fajarlabs/PROJECT_FloodMonitoring/BOX_PANEL2.jpeg

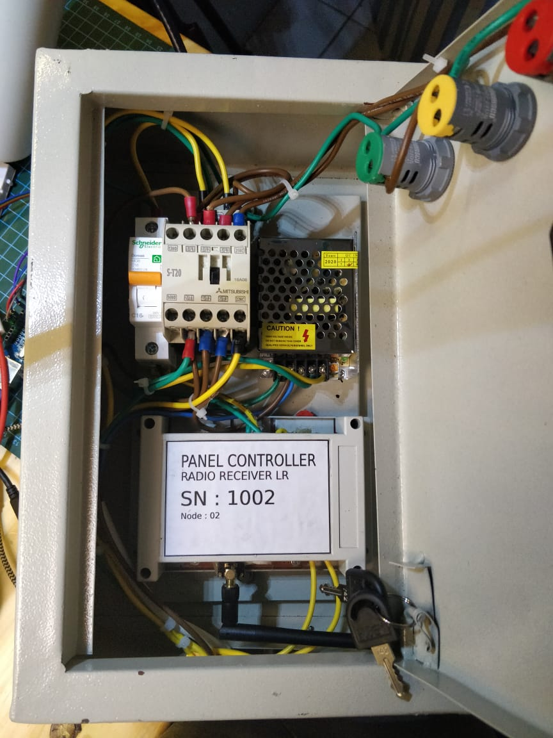
BOX_PANEL2.jpeg
