fajarlabs/PROJECT_FloodMonitoring/BOX_PANEL_FLASH.jpeg

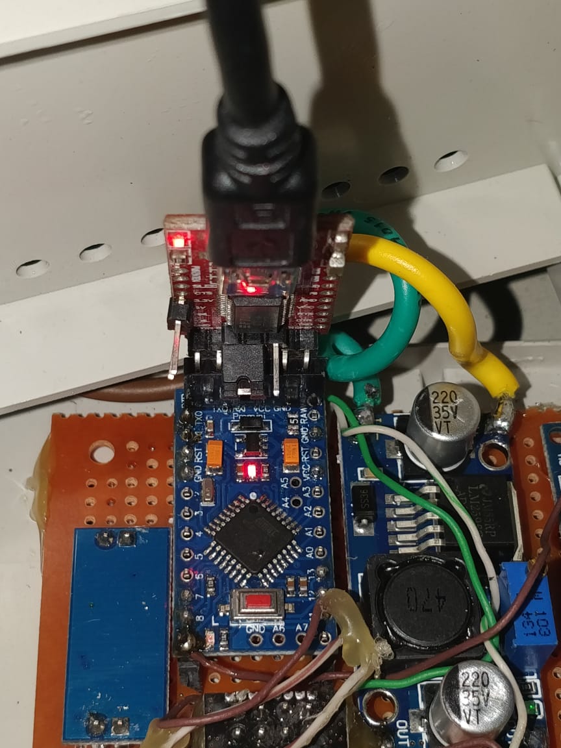
BOX_PANEL_FLASH.jpeg
