fajarlabs/PROJECT_FloodMonitoring/CEK TIMEOUT.png

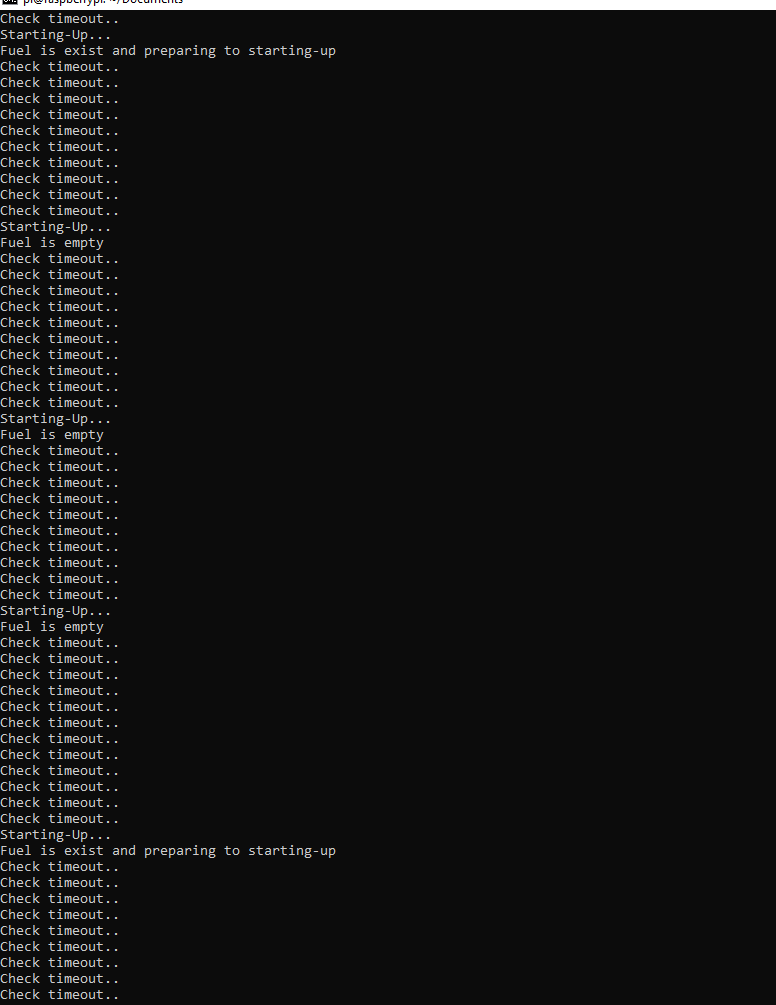
CEK TIMEOUT.png
