fajarlabs/PROJECT_FloodMonitoring/check_timout.png

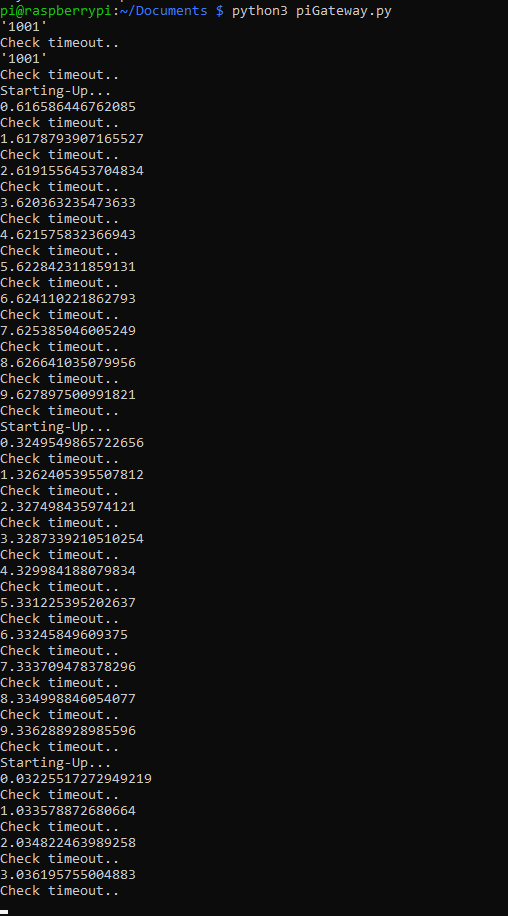
check_timout.png
