fajarlabs/PROJECT_FloodMonitoring/CommandPush.png

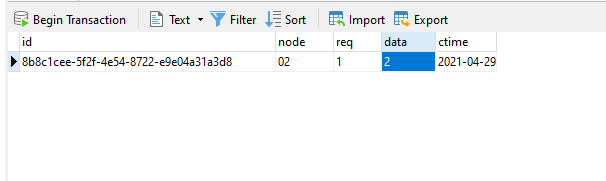
CommandPush.png
