fajarlabs/PROJECT_FloodMonitoring/dataLogController.png

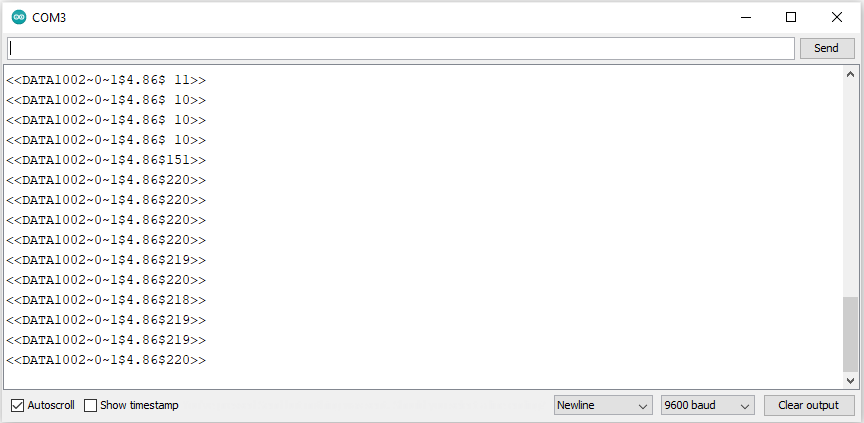
dataLogController.png
