fajarlabs/PROJECT_FloodMonitoring/DB_POSTGRES.png

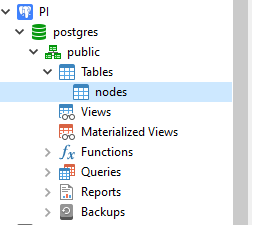
DB_POSTGRES.png
