fajarlabs/PROJECT_FloodMonitoring/Fritzing/COMMAND_CENTER_bb.png

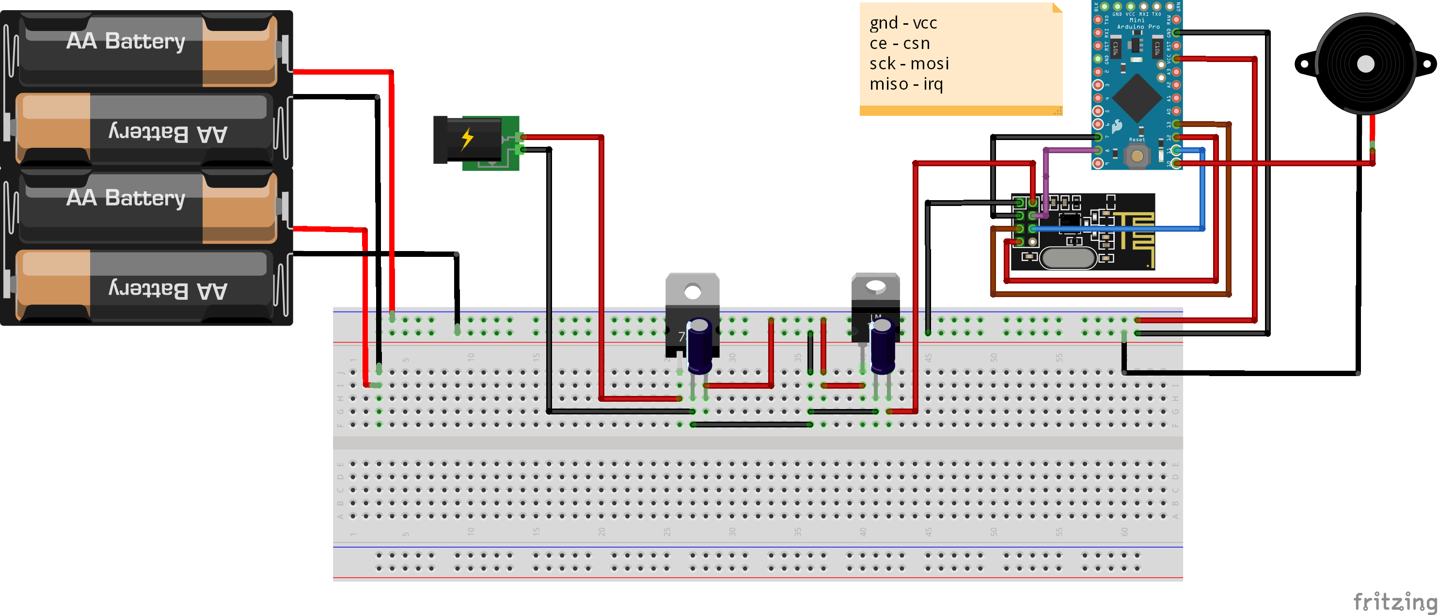
Fritzing/COMMAND_CENTER_bb.png
