fajarlabs/PROJECT_FloodMonitoring/Fritzing/FLOAT_SENSOR.png

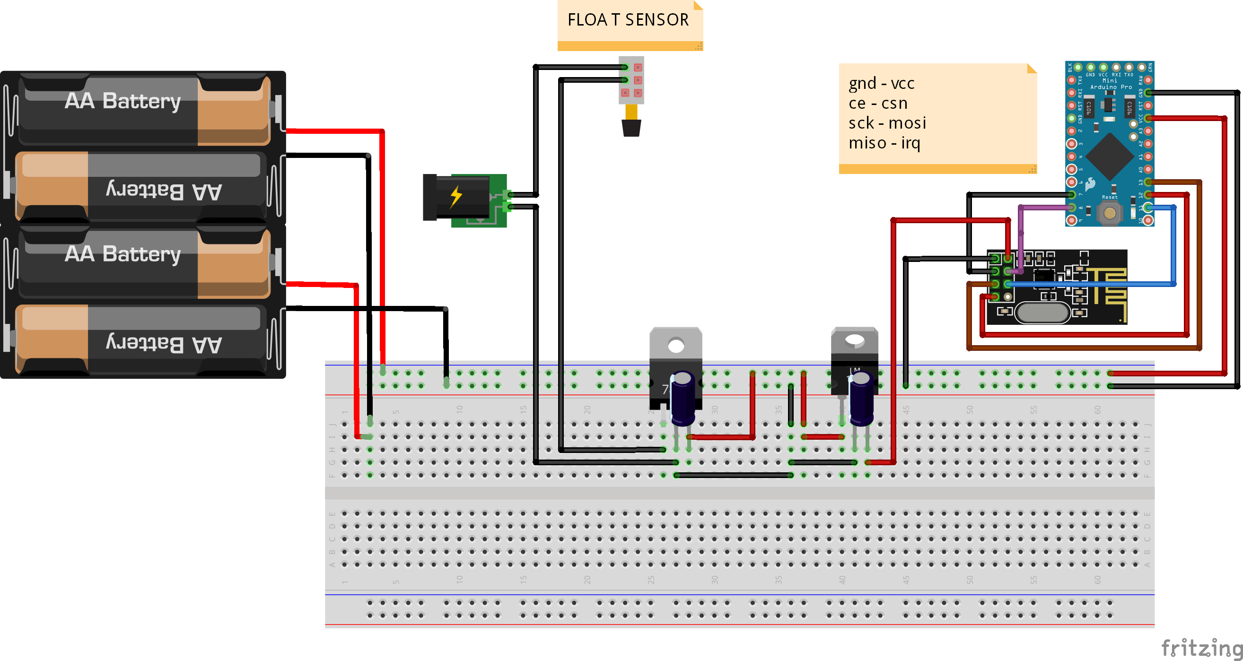
Fritzing/FLOAT_SENSOR.png
