fajarlabs/PROJECT_FloodMonitoring/Fritzing/PANEL_CONTROLLER_bb.png

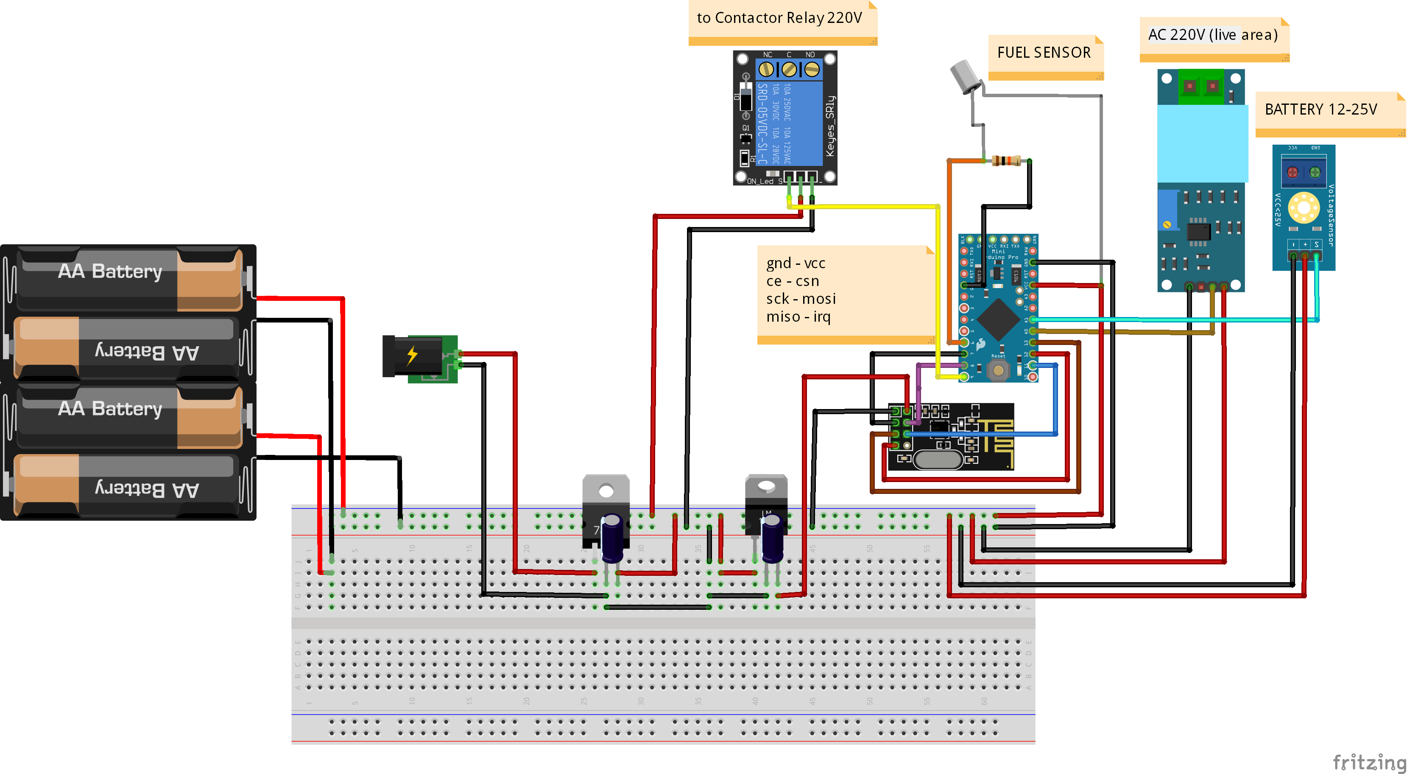
Fritzing/PANEL_CONTROLLER_bb.png
