fajarlabs/PROJECT_FloodMonitoring/SENSOR_FLOAT2.jpeg

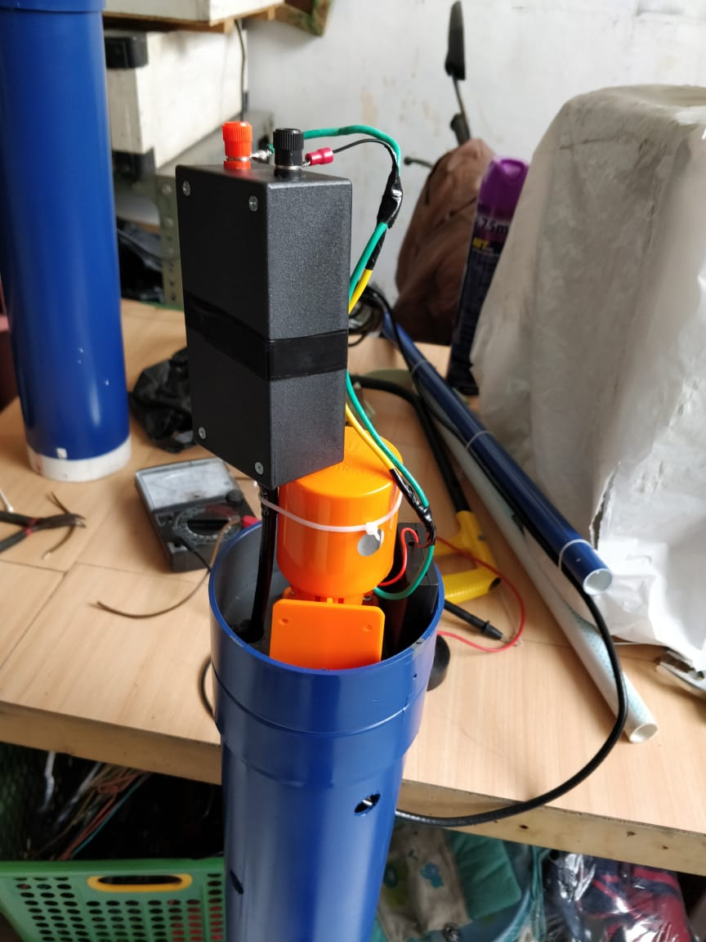
SENSOR_FLOAT2.jpeg
