fajarlabs/PROJECT_FloodMonitoring/SENSOR_FLOAT4.jpeg

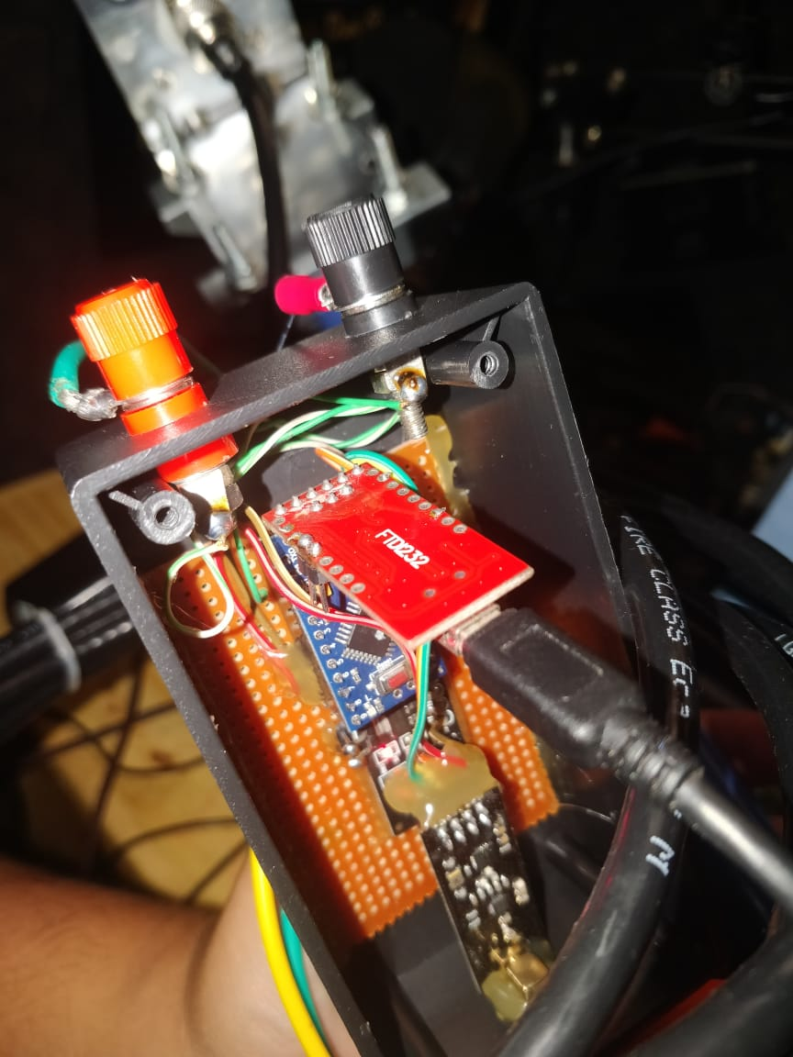
SENSOR_FLOAT4.jpeg
