fajarlabs/PROJECT_FloodMonitoring/SENSOR_FLOAT5.jpeg

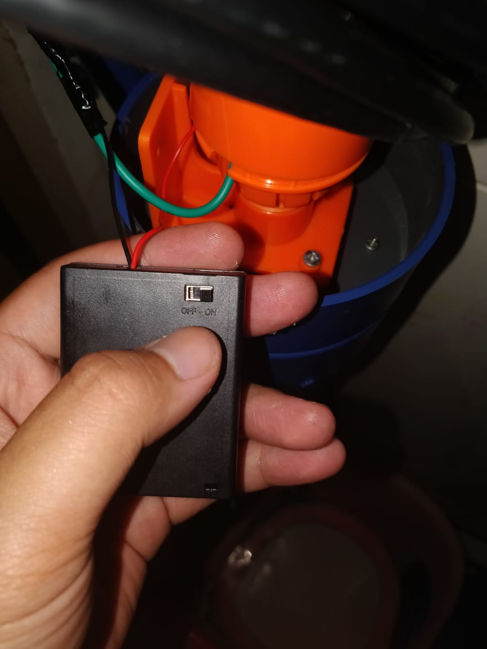
SENSOR_FLOAT5.jpeg
