fajarlabs/PROJECT_FloodMonitoring/SENSOR_FLOAT.jpeg

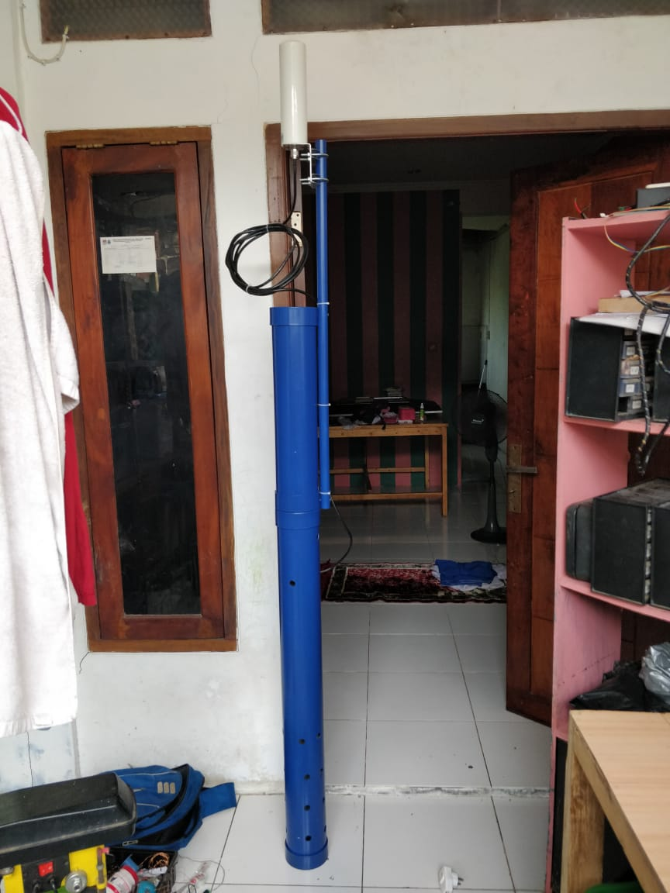
SENSOR_FLOAT.jpeg
