fajarlabs/PROJECT_FloodMonitoring/SensorMonitor.png

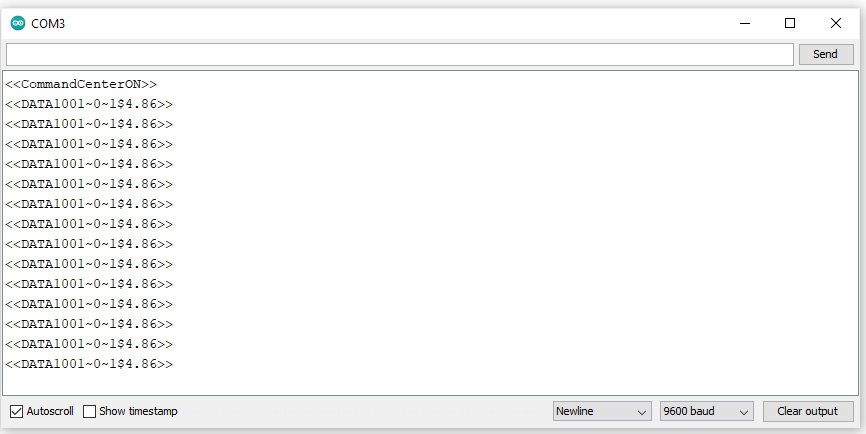
SensorMonitor.png
