fajarlabs/PROJECT_FloodMonitoring/signal.png

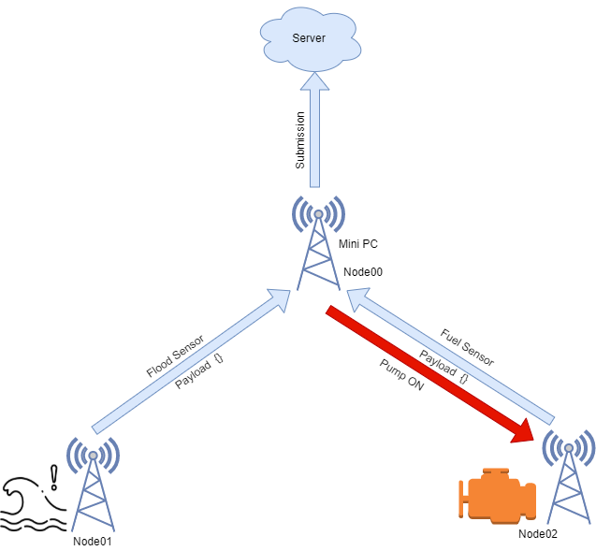
signal.png
