fajarlabs/PROJECT_FloodMonitoring/Tahap II/Edit Account MQTT.png

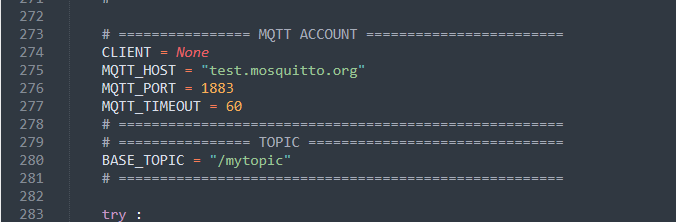
Tahap II/Edit Account MQTT.png
