fajarlabs/PROJECT_FloodMonitoring/Tahap II/FormatCode.png

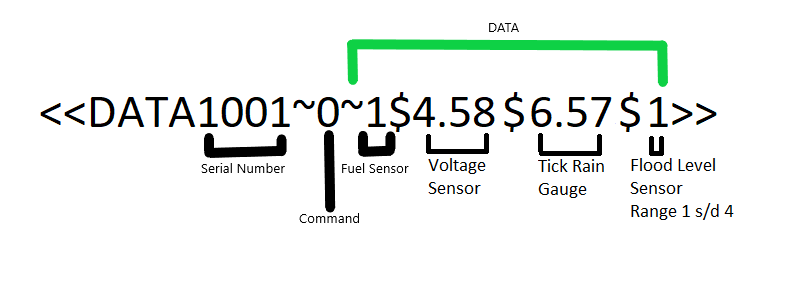
Tahap II/FormatCode.png
