fajarlabs/PROJECT_FloodMonitoring/Tahap II/mosquitto_sub.png

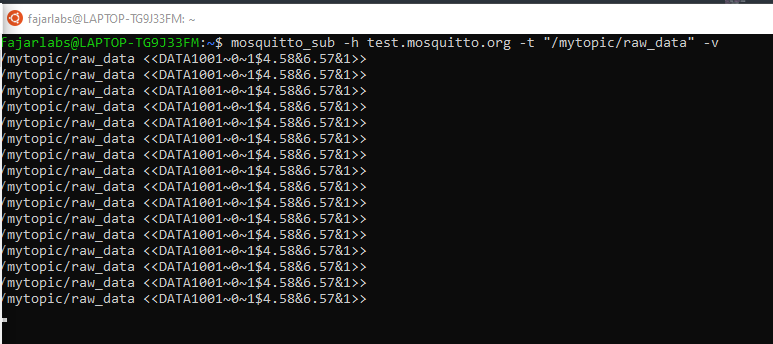
Tahap II/mosquitto_sub.png
