fajarlabs/PROJECT_FloodMonitoring/Tahap II/PCB_Interface.JPG

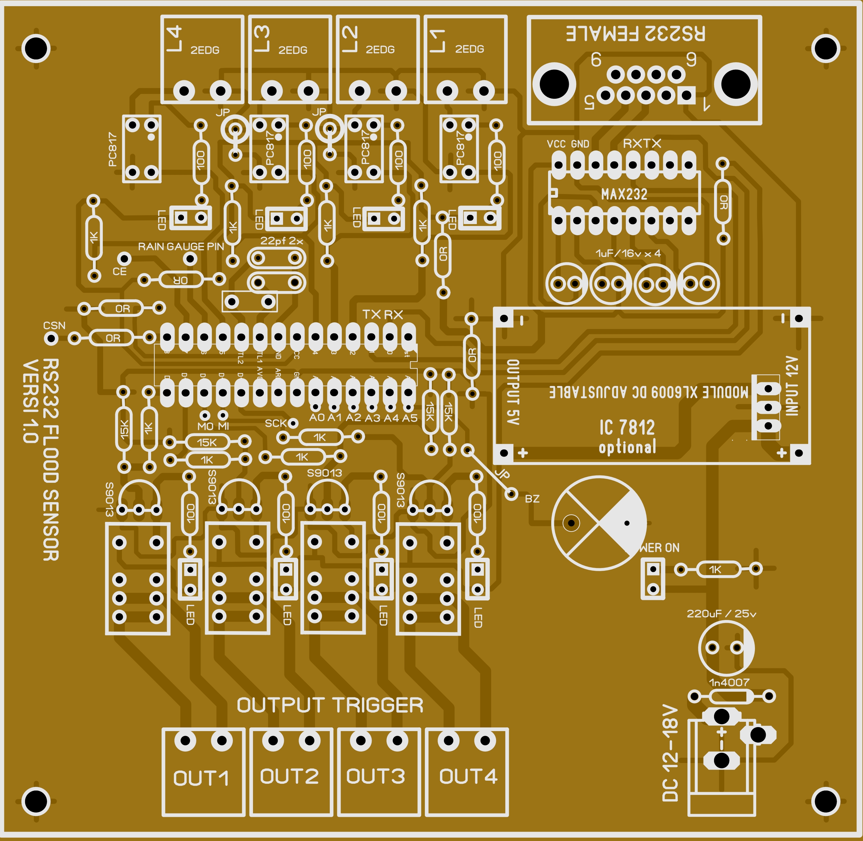
Tahap II/PCB_Interface.JPG
