fajarlabs/PROJECT_FloodMonitoring/Tahap II/PiGatewayBroadcastMQTT.png

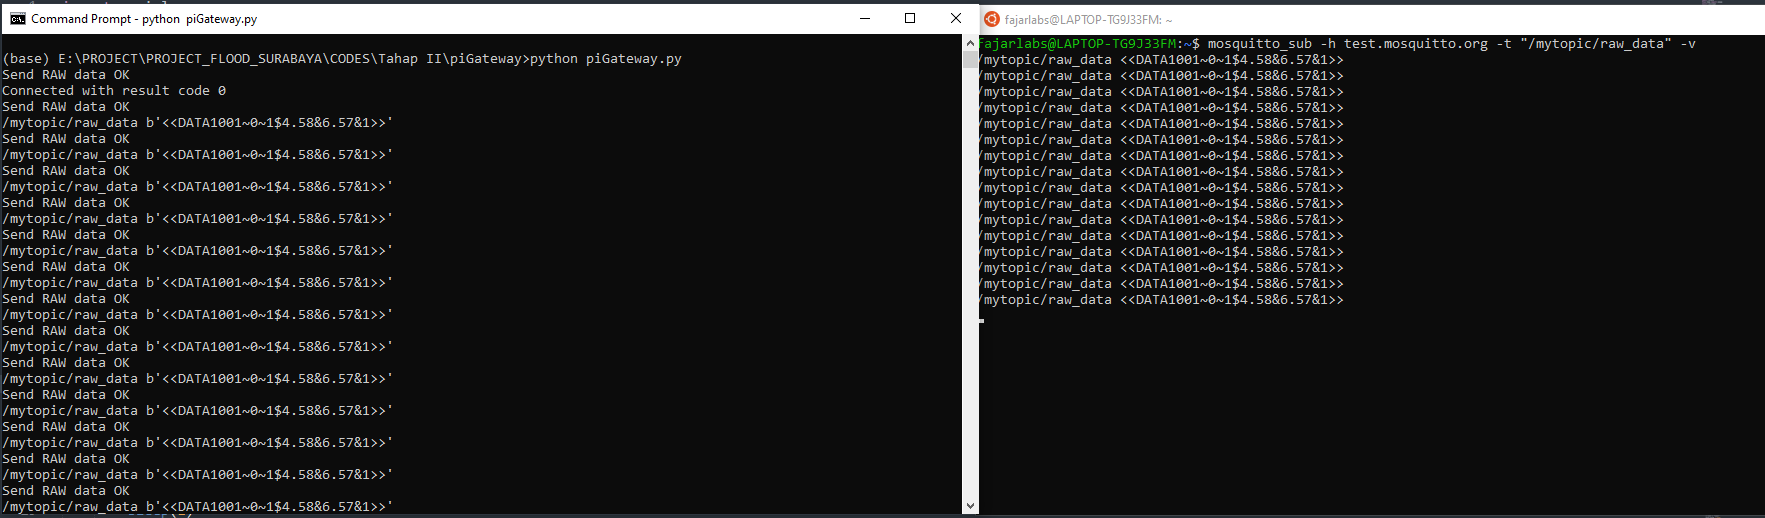
Tahap II/PiGatewayBroadcastMQTT.png
