fajarlabs/PROJECT_FloodMonitoring/Tahap II/USB-ASP.jpg

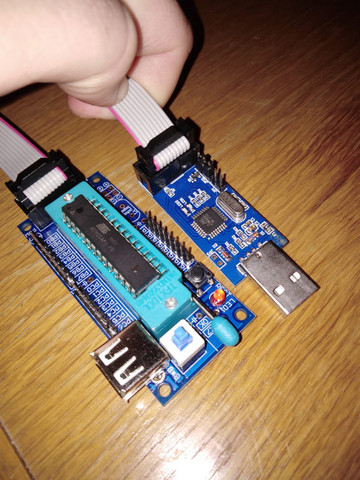
Tahap II/USB-ASP.jpg
