fajarlabs/PROJECT_FloodMonitoring/Tahap II/WhatsApp Image 2021-06-20 at 11.57.32 PM (1).jpeg

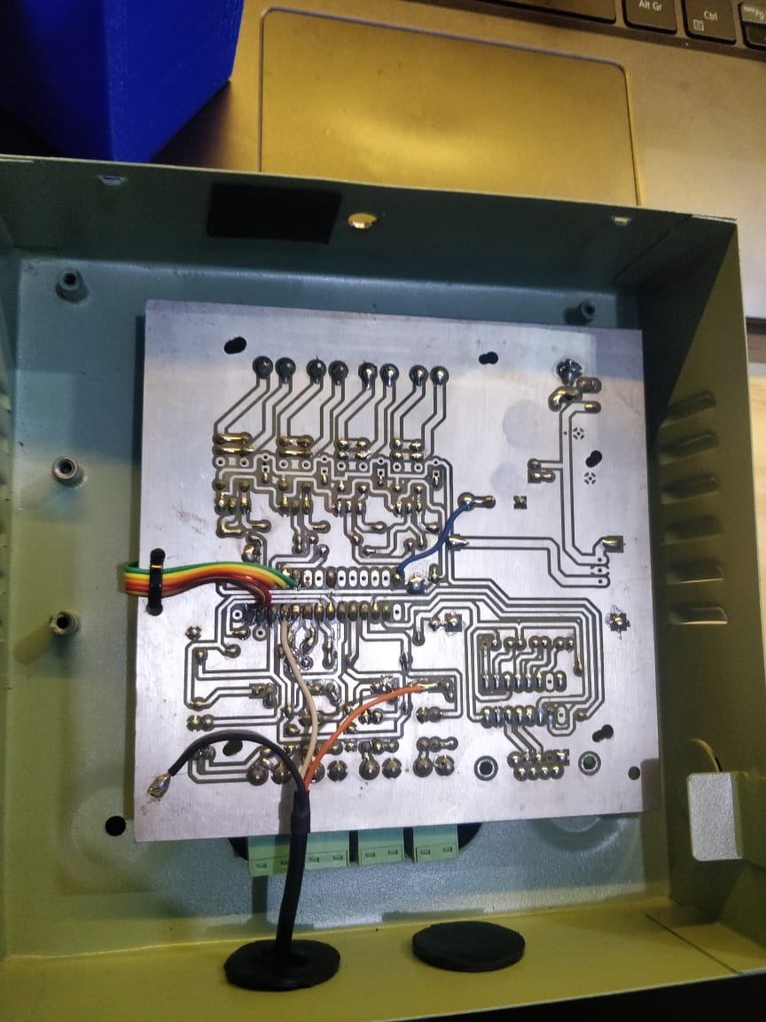
Tahap II/WhatsApp Image 2021-06-20 at 11.57.32 PM (1).jpeg
