fajarlabs/PROJECT_FloodMonitoring/WhatsApp Image 2021-04-11 at 10.38.35 PM.jpeg

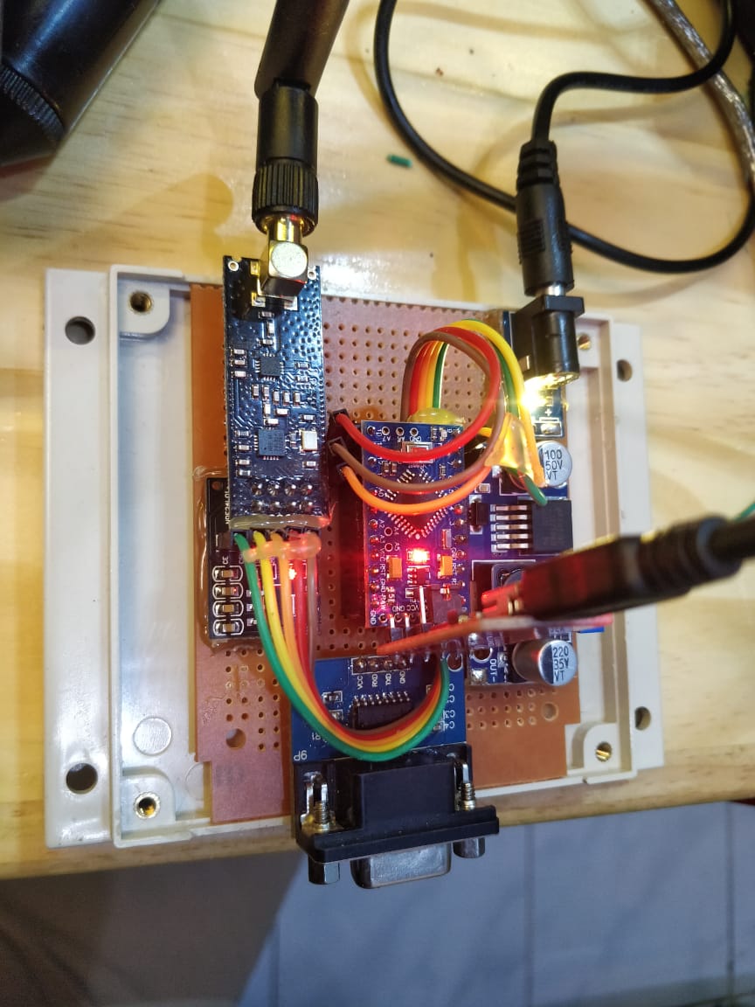
WhatsApp Image 2021-04-11 at 10.38.35 PM.jpeg
