fajarlabs/PROJECT_FloodMonitoring/WhatsApp Image 2021-04-11 at 10.44.52 PM.jpeg

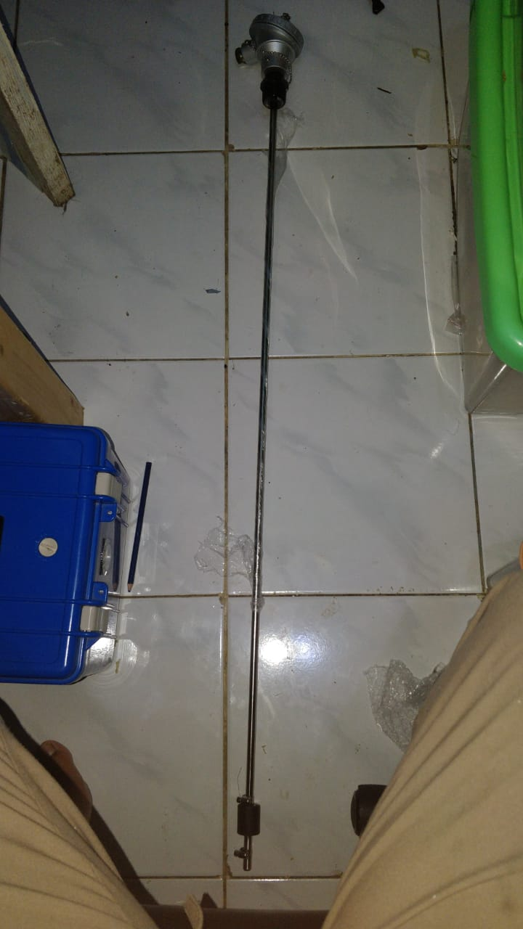
WhatsApp Image 2021-04-11 at 10.44.52 PM.jpeg
