fajarlabs/PROJECT_FloodMonitoring/WhatsApp Image 2021-04-11 at 10.45.41 PM.jpeg

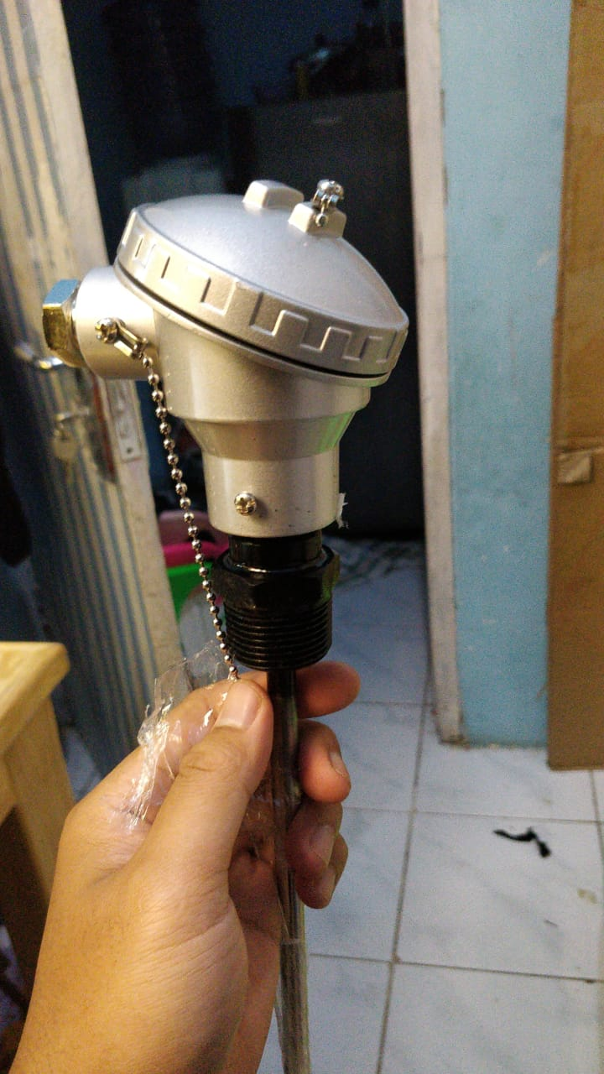
WhatsApp Image 2021-04-11 at 10.45.41 PM.jpeg
