fajarlabs/PROJECT_FloodMonitoring/WhatsApp Image 2021-04-12 at 5.15.50 PM.jpeg

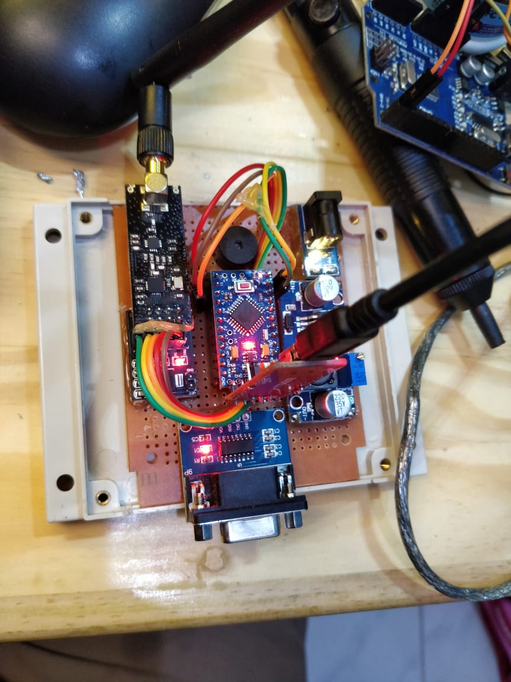
WhatsApp Image 2021-04-12 at 5.15.50 PM.jpeg
