fajarlabs/PROJECT_FloodMonitoring/WhatsApp Image 2021-04-13 at 5.51.59 PM.jpeg

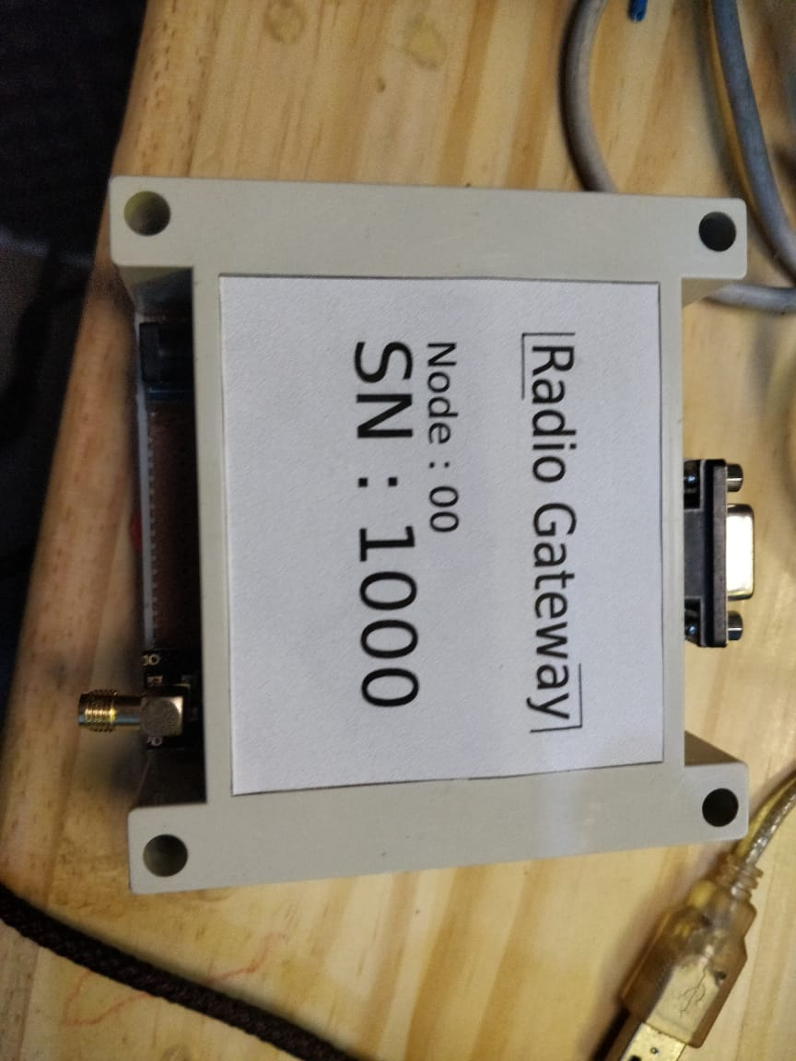
WhatsApp Image 2021-04-13 at 5.51.59 PM.jpeg
