fajarlabs/PROJECT_FloodMonitoring/WhatsApp Image 2021-04-13 at 5.54.51 PM.jpeg

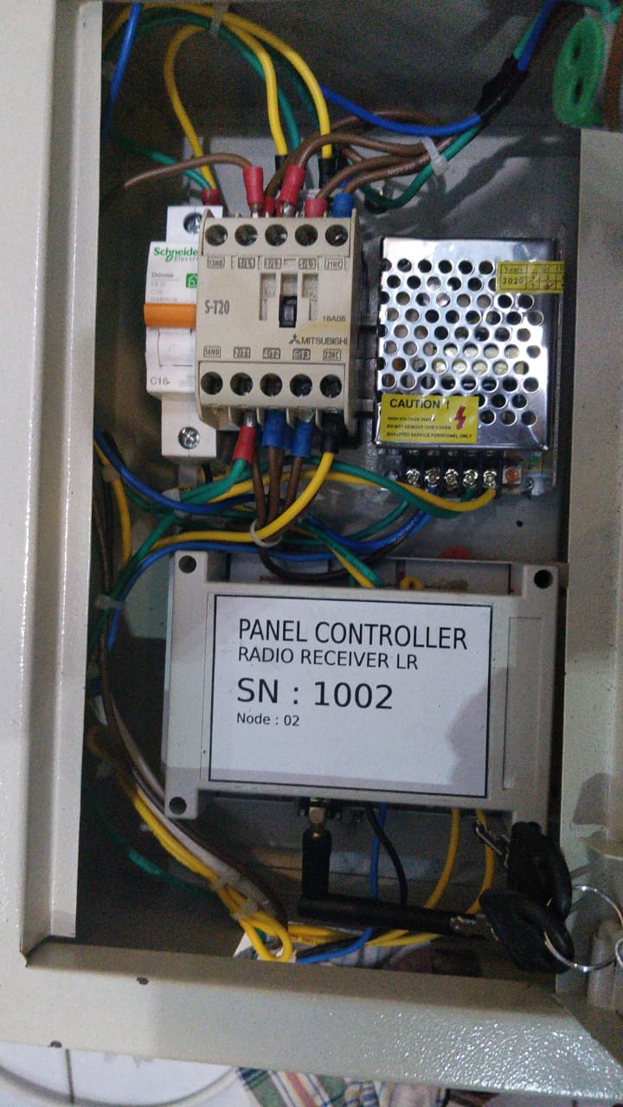
WhatsApp Image 2021-04-13 at 5.54.51 PM.jpeg
