fajarlabs/PROJECT_FloodMonitoring/ResultAllData.png

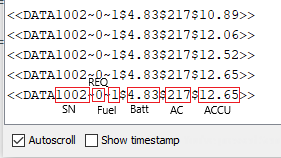
ResultAllData.png
