fajarlabs/PROJECT_FloodMonitoring/Tahap II/DebugMQTT.png

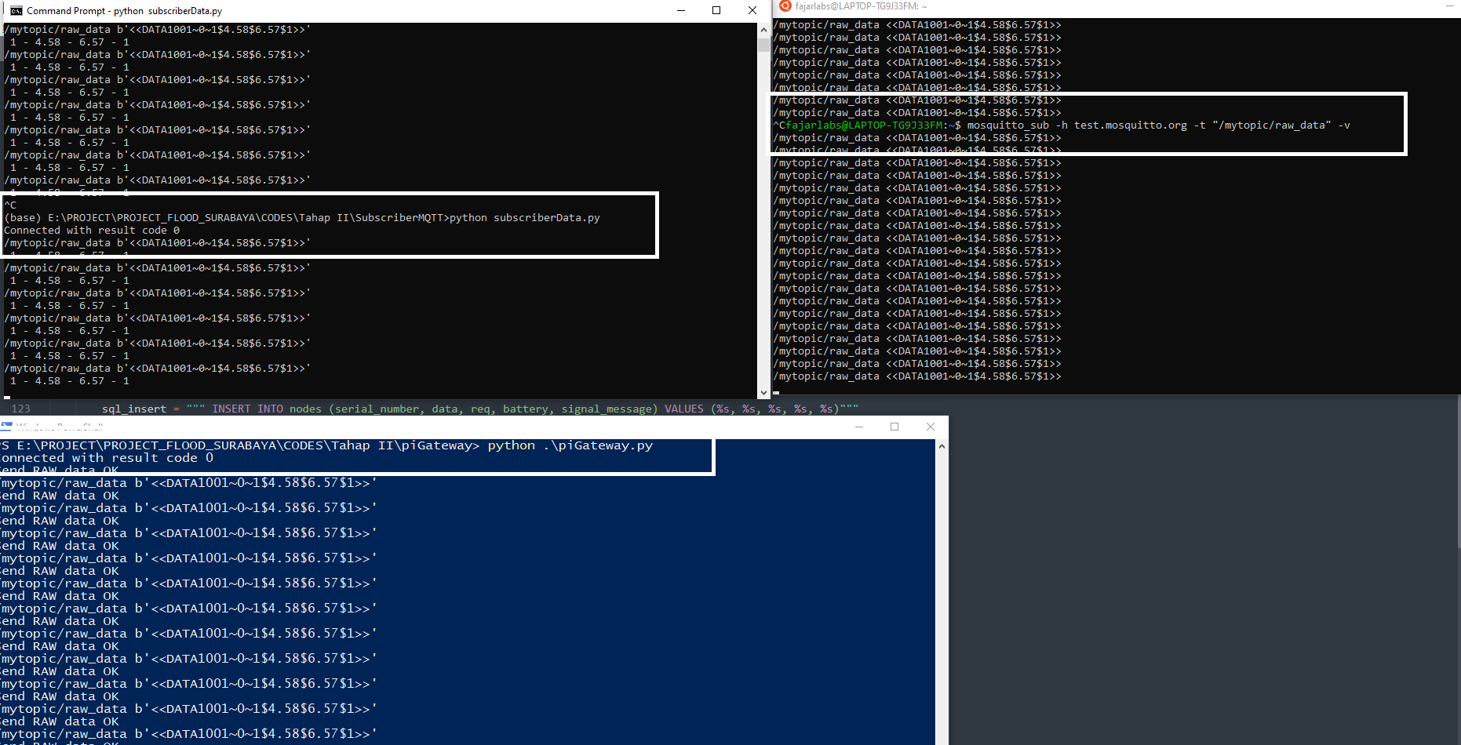
Tahap II/DebugMQTT.png
